dombeef/pockeTETRIS/images/image2.jpg

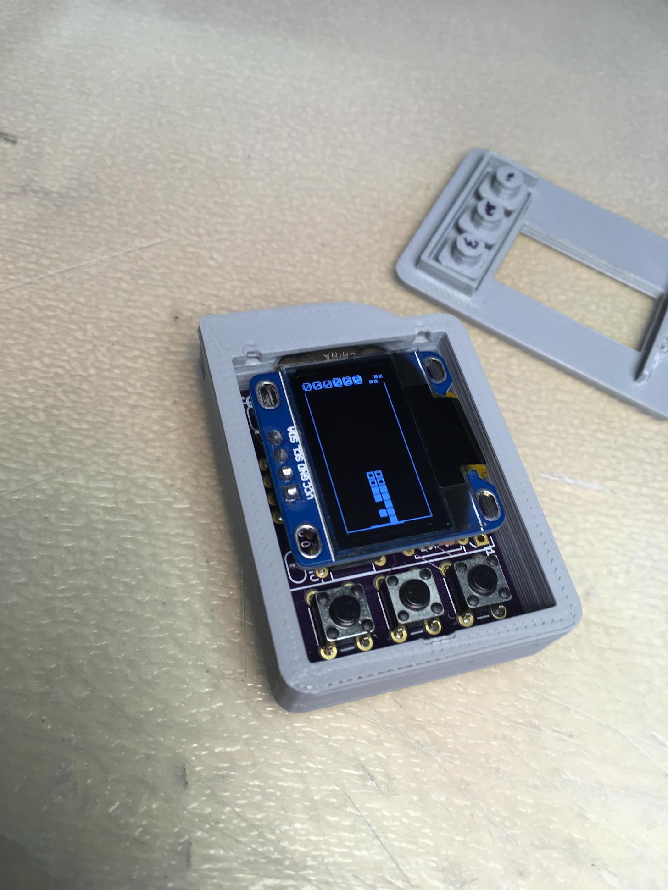
images/image2.jpg
