dombeef/pockeTETRIS/images/image3.jpg

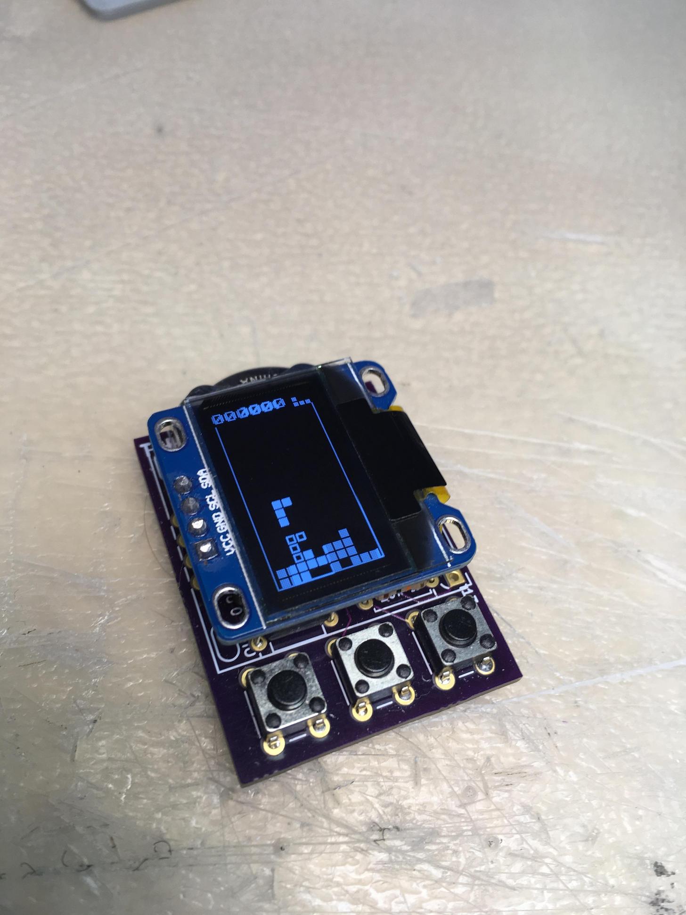
images/image3.jpg
